thestumbler/buspirate5-hardware-mechanical/enclosure/test.scad

include <ref.scad>
//use <enc.scad>

color("green")
fiducial([40,10,0]);
echo( fid_thk, fid_thk );
